man0n0n0/TOF_drawer/hardware/00cnc_cutting.dxf

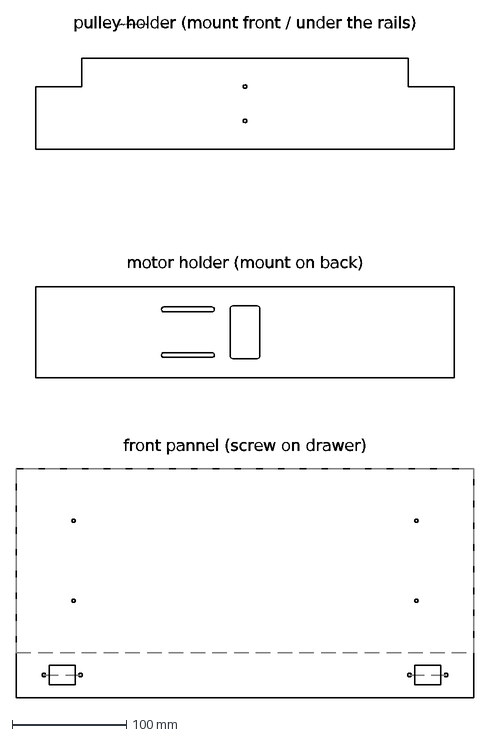
[picture p15: CAD file, 2025-05-28]
hardware/00cnc_cutting.dxf
pulley holder (front / under the rails)
pulley holder (mount front / under the rails)
motor holder (mount on back)
front pannel (screw on drawer)
