man0n0n0/TOF_drawer/hardware/01GT5belttensionner-BodyChamfer.stl

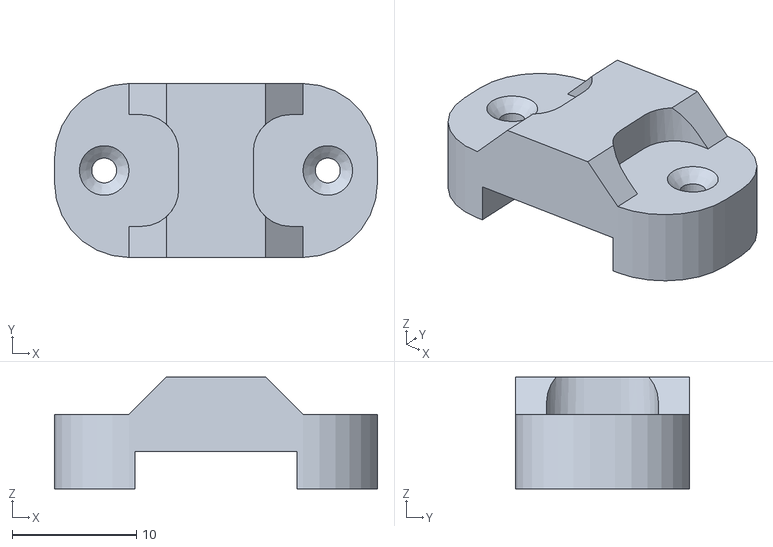
[picture p16: CAD file, 2025-05-28]
hardware/01GT5belttensionner-BodyChamfer.stl
26.0 x 14.0 x 9.00
