man0n0n0/TOF_drawer/hardware/02GT5belttensionner.FCStd

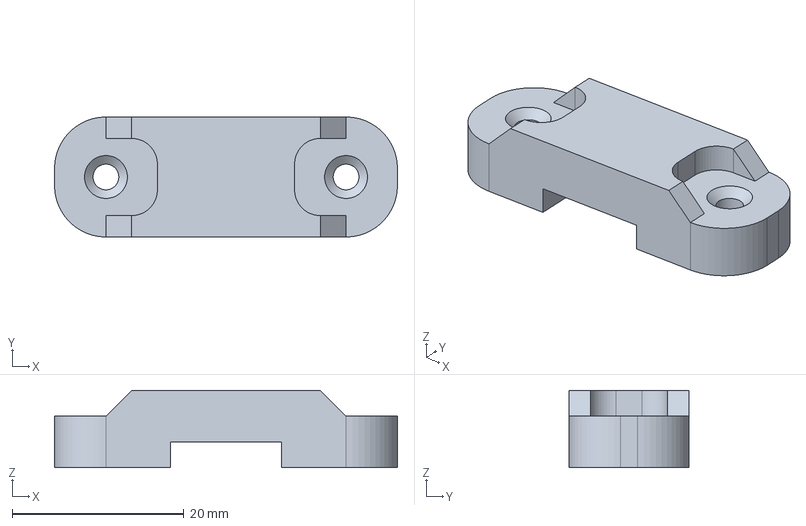
[picture p17: CAD file, 2025-05-28]
hardware/02GT5belttensionner.FCStd
40.0 x 14.0 x 9.00 mm
