man0n0n0/TOF_drawer/hardware/ld2410_magnetholder.FCStd

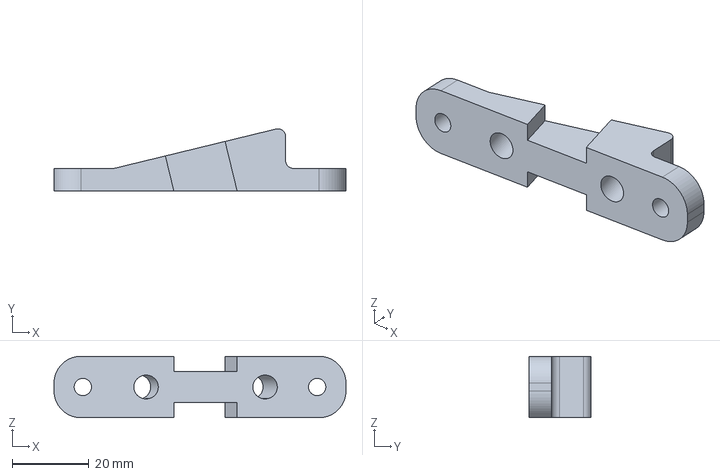
[picture p18: CAD file, 2025-05-28]
hardware/ld2410_magnetholder.FCStd
76.0 x 16.2 x 16.0 mm
