man0n0n0/TOF_drawer/hardware/driver_mount-BodyMirrored.stl

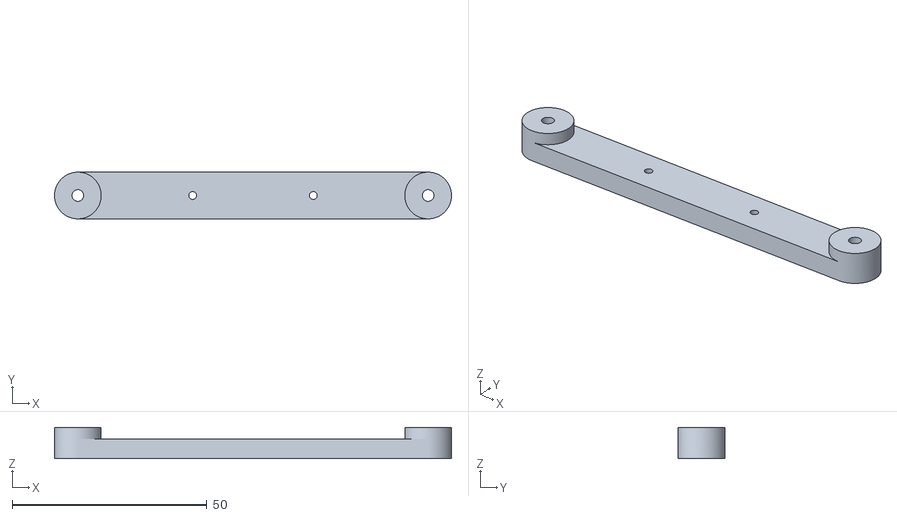
[picture p19: CAD file, 2025-05-21]
hardware/driver_mount-BodyMirrored.stl
102.0 x 12.0 x 8.00
