man0n0n0/TOF_drawer/hardware/ld2410_magnetholder-Body.stl

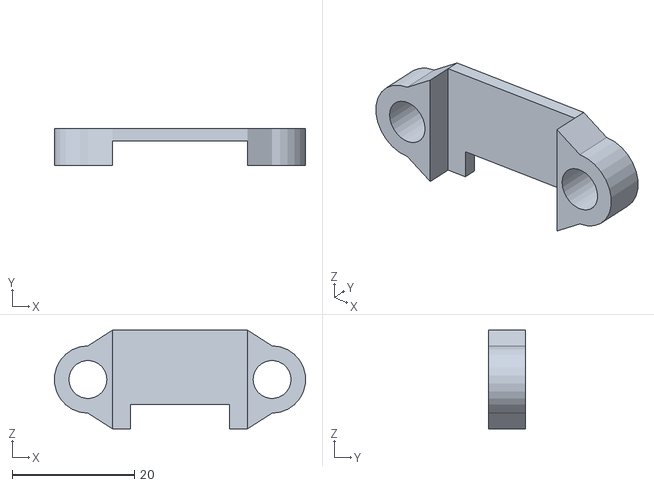
[picture p20: CAD file, 2025-05-20]
hardware/ld2410_magnetholder-Body.stl
41.0 x 6.00 x 16.1
