man0n0n0/TOF_drawer/hardware/pcb_mount.FCStd

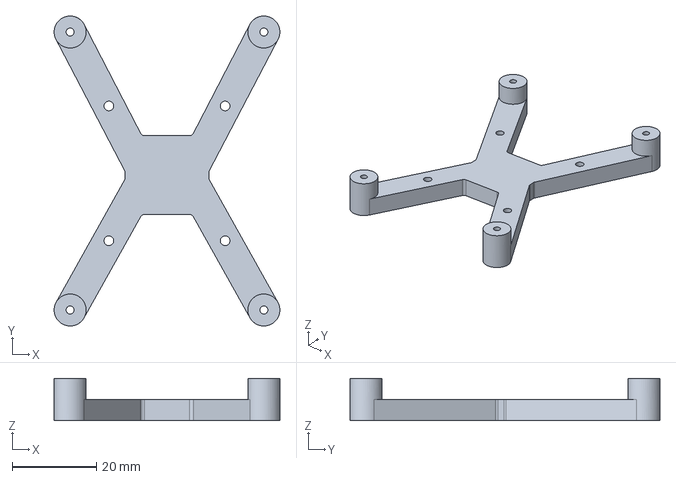
[picture p21: CAD file, 2025-05-19]
hardware/pcb_mount.FCStd
53.6 x 73.6 x 10.0 mm
