man0n0n0/TOF_drawer/hardware/dmt332t_mount-Body.stl

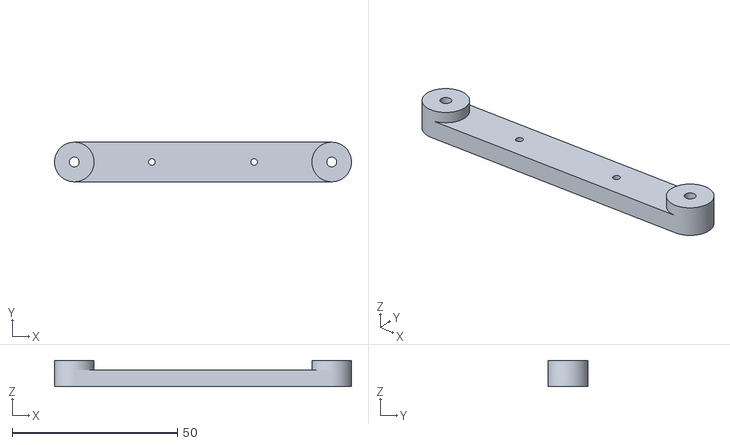
[picture p22: CAD file, 2025-05-17]
hardware/dmt332t_mount-Body.stl
90.0 x 12.0 x 8.00
