man0n0n0/TOF_drawer/hardware/ld2410_magnetholder-Body002Pad002.stl

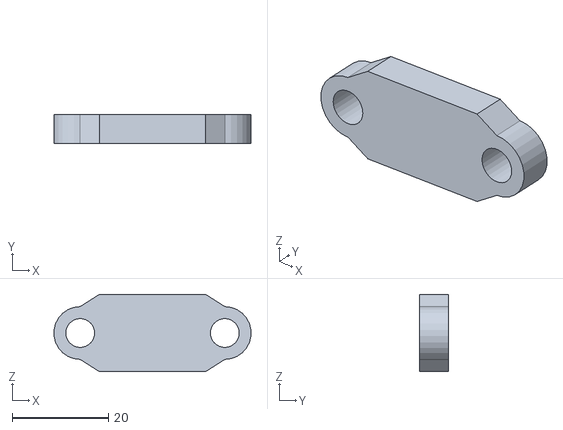
[picture p23: CAD file, 2025-05-17]
hardware/ld2410_magnetholder-Body002Pad002.stl
41.0 x 6.00 x 16.1
