man0n0n0/TOF_drawer/hardware/ld2410_magnetholder-Body001.stl

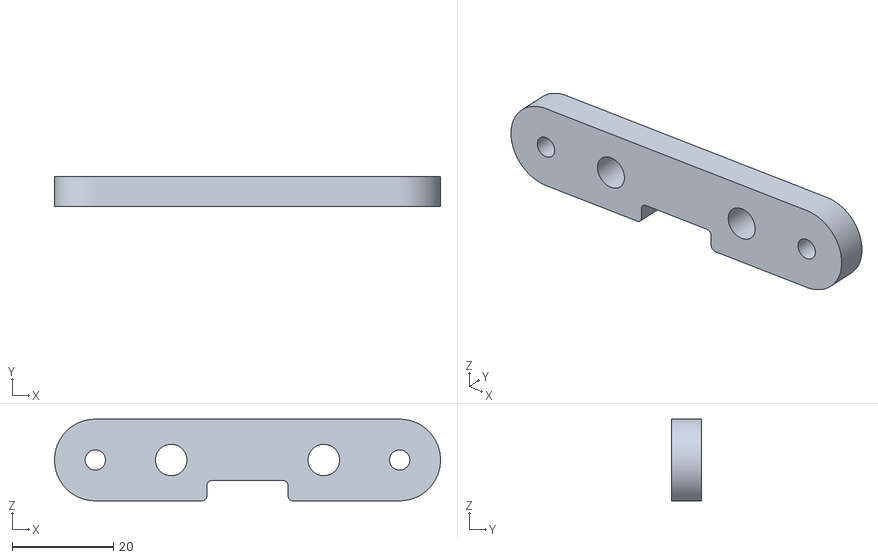
[picture p24: CAD file, 2025-05-17]
hardware/ld2410_magnetholder-Body001.stl
76.1 x 6.00 x 16.1
