man0n0n0/TOF_drawer/hardware/ld2410_magnetholder-Body002.stl

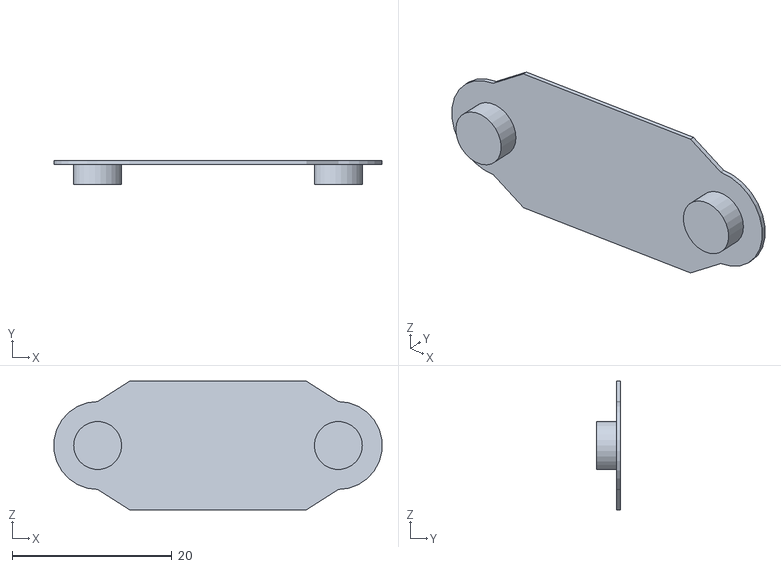
[picture p25: CAD file, 2025-05-17]
hardware/ld2410_magnetholder-Body002.stl
41.0 x 3.00 x 16.1
