man0n0n0/TOF_drawer/hardware/dmt332t_mount-BodyMirrored.stl

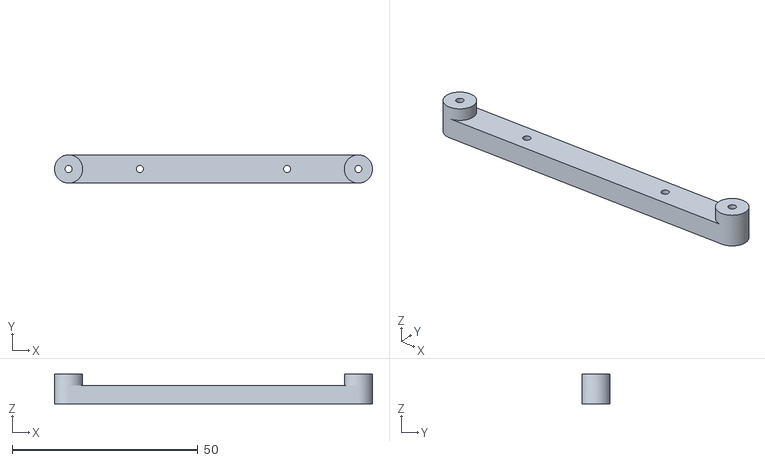
[picture p26: CAD file, 2025-05-17]
hardware/dmt332t_mount-BodyMirrored.stl
85.6 x 7.60 x 8.00
