man0n0n0/TOF_drawer/hardware/ld2410_magnetholder-BodyPad.stl

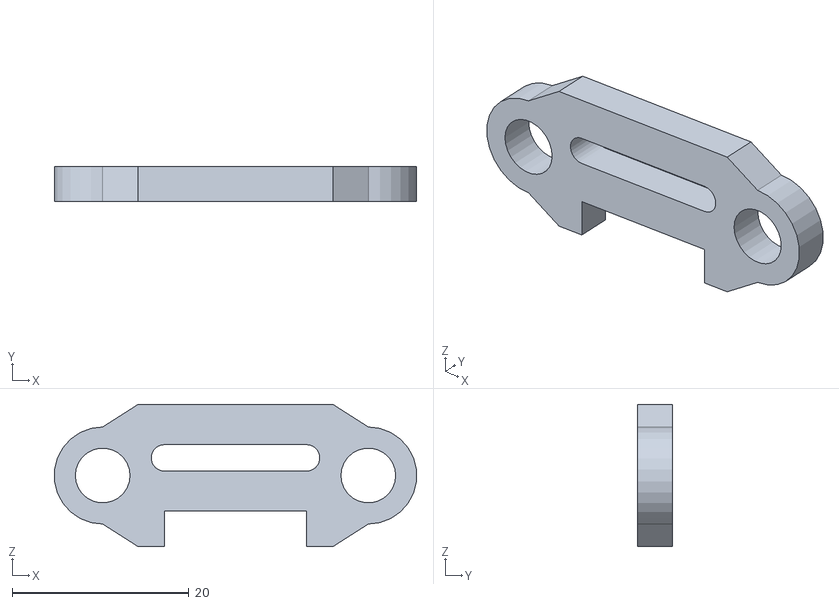
[picture p27: CAD file, 2025-05-15]
hardware/ld2410_magnetholder-BodyPad.stl
41.0 x 4.00 x 16.1
