man0n0n0/TOF_drawer/hardware/00pcb_mount.stl

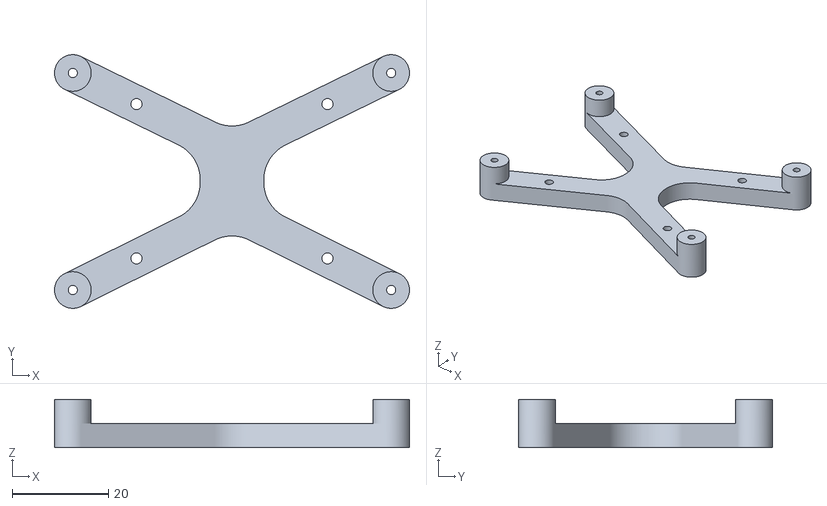
[picture p28: CAD file, 2025-05-14]
hardware/00pcb_mount.stl
73.6 x 52.6 x 10.0
