man0n0n0/TOF_drawer/hardware/derivation_box.FCStd

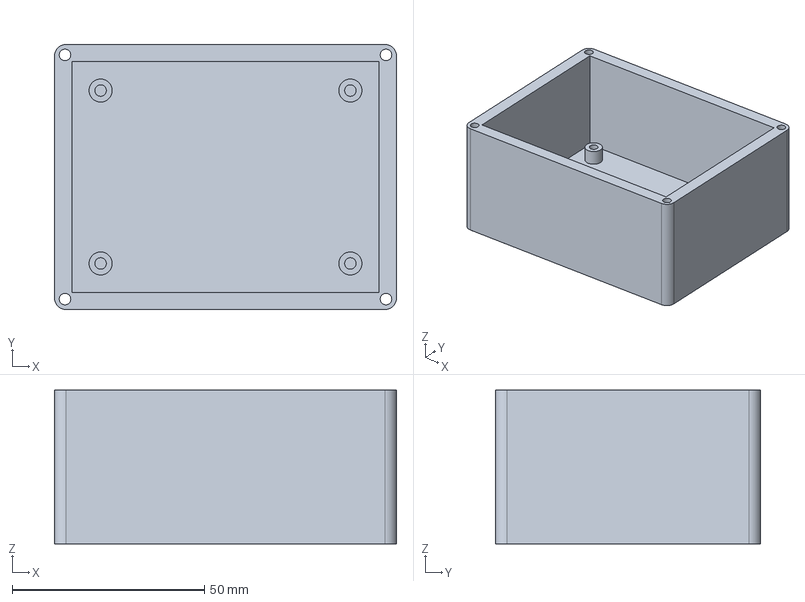
[picture p29: CAD file, 2025-04-07]
hardware/derivation_box.FCStd
89.0 x 69.0 x 40.0 mm
