man0n0n0/TOF_drawer/hardware/parametric_derivation_box.FCStd

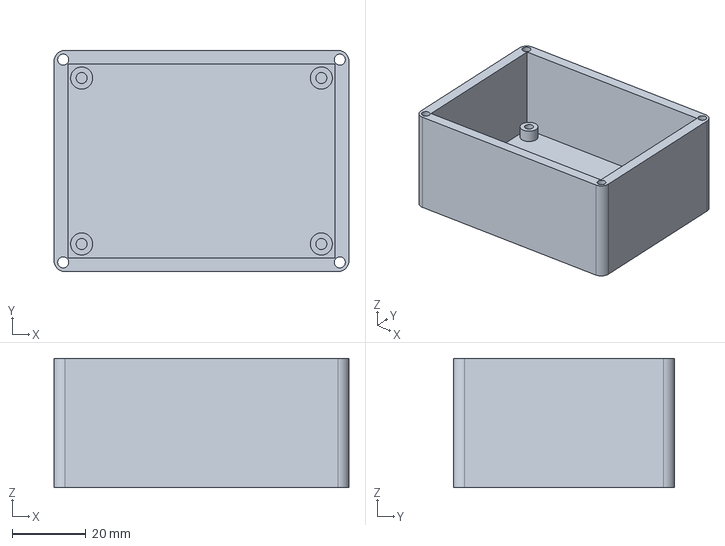
[picture p30: CAD file, 2025-04-07]
hardware/parametric_derivation_box.FCStd
80.0 x 60.0 x 35.0 mm
