man0n0n0/TOF_drawer/hardware/00GT5belt_tensioner_m5insert.FCStd

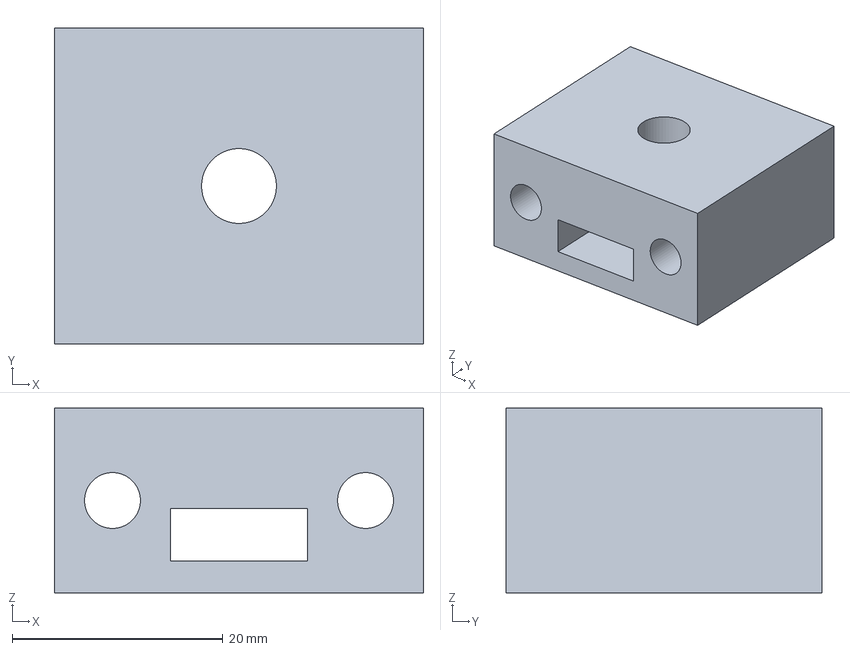
[picture p32: CAD file, 2025-04-04]
hardware/00GT5belt_tensioner_m5insert.FCStd
35.0 x 30.0 x 17.5 mm
