man0n0n0/TOF_drawer/hardware/00end_switch-Body.stl

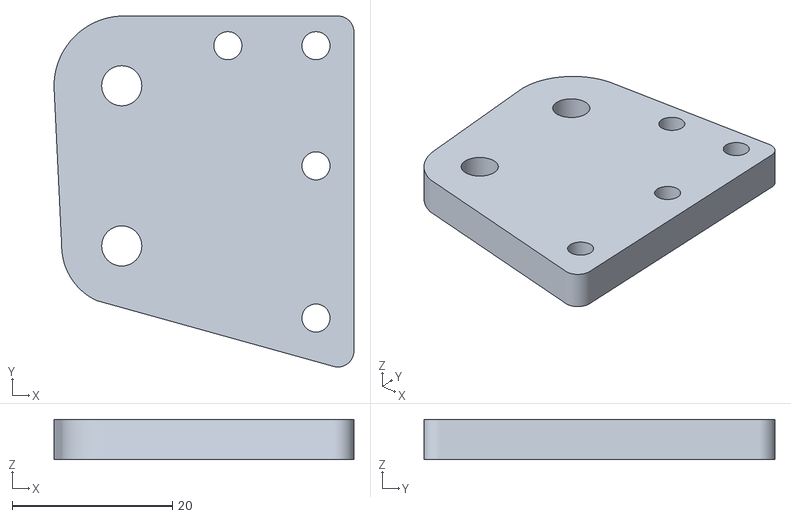
[picture p33: CAD file, 2025-04-04]
hardware/00end_switch-Body.stl
37.4 x 43.8 x 5.00
