man0n0n0/TOF_drawer/hardware/00GT5belt_tensioner_fixedpart_m5insert-Body.stl

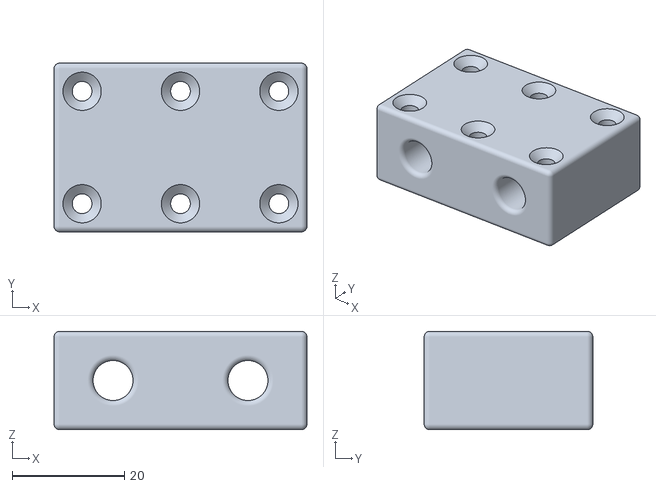
[picture p35: CAD file, 2025-04-04]
hardware/00GT5belt_tensioner_fixedpart_m5insert-Body.stl
45.0 x 30.0 x 17.5
