man0n0n0/TOF_drawer/hardware/01GT5belt_fix_m5insert.FCStd

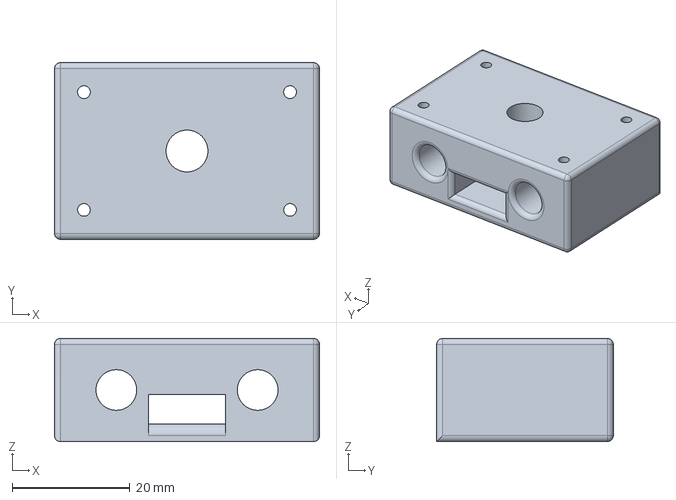
[picture p36: CAD file, 2025-04-04]
hardware/01GT5belt_fix_m5insert.FCStd
45.0 x 30.0 x 17.5 mm
