man0n0n0/TOF_drawer/hardware/02nema23_bracket_offsettirroirt.stl

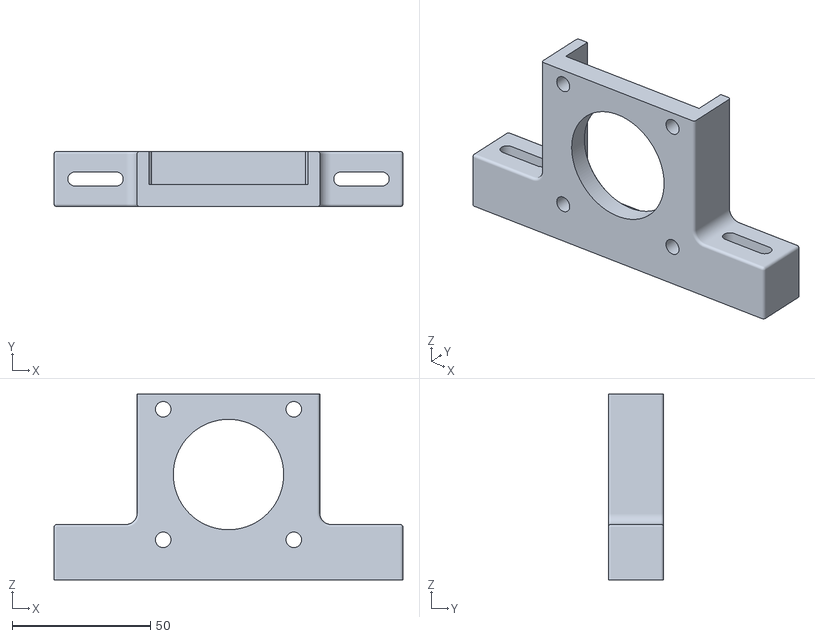
[picture p37: CAD file, 2025-04-03]
hardware/02nema23_bracket_offsettirroirt.stl
126.0 x 20.0 x 67.0
