man0n0n0/TOF_drawer/hardware/00nema23_bracket_offsettirroir.FCStd

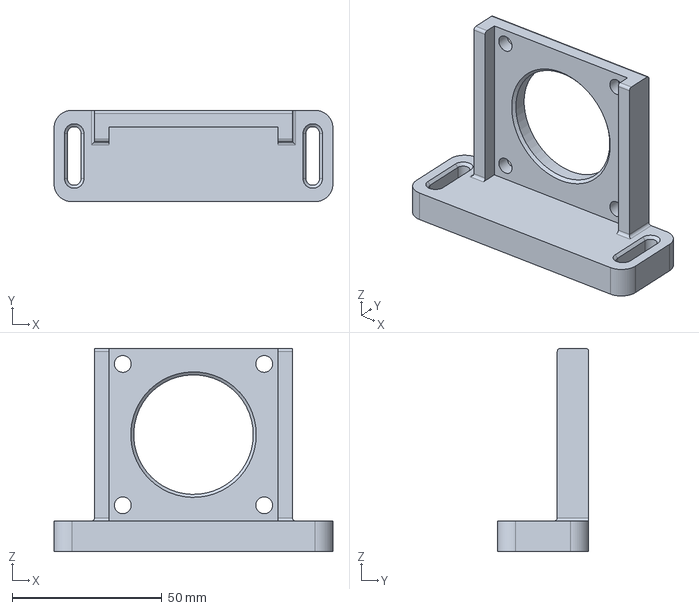
[picture p38: CAD file, 2025-04-03]
hardware/00nema23_bracket_offsettirroir.FCStd
93.0 x 30.5 x 67.8 mm
