man0n0n0/TOF_drawer/hardware/01nema23_bracket_offsettirroir.FCStd

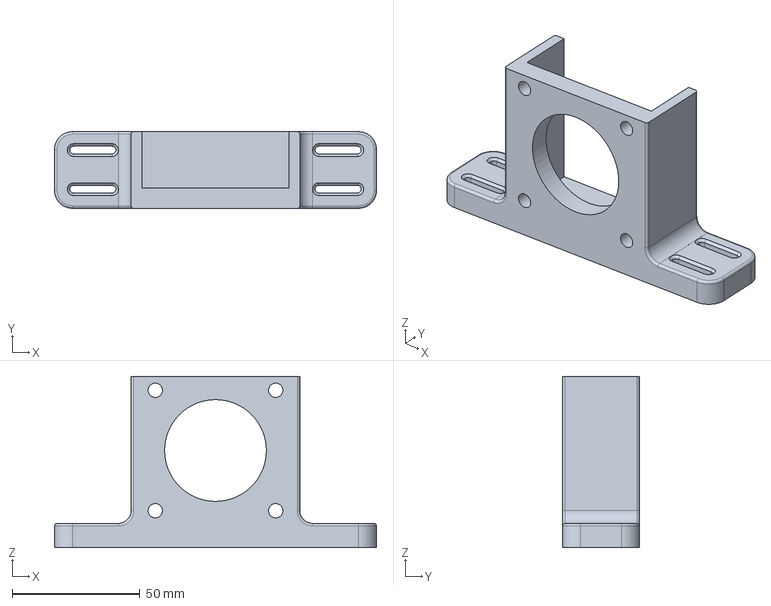
[picture p39: CAD file, 2025-04-03]
hardware/01nema23_bracket_offsettirroir.FCStd
126.0 x 30.0 x 67.0 mm
