man0n0n0/TOF_drawer/hardware/00_pulley_holder_meutriere.FCStd

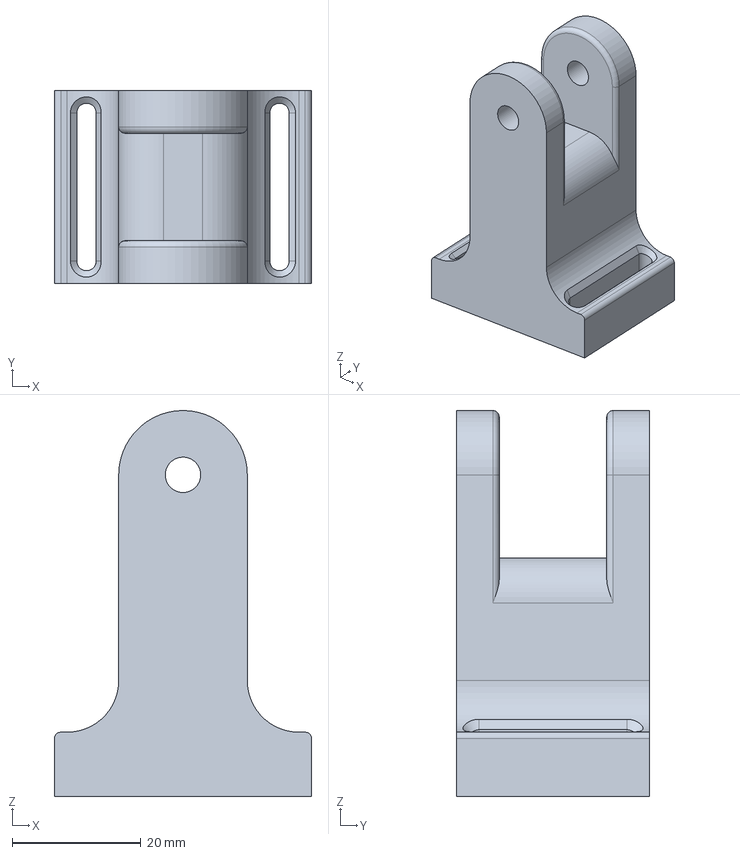
[picture p40: CAD file, 2025-04-02]
hardware/00_pulley_holder_meutriere.FCStd
40.0 x 30.0 x 60.0 mm
